danchouzhou/003Clock/firmware/ISP_UART1/isp_uart1.h

#define trig_IAPGO           TA=0xAA;TA=0x55;IAPTRG|=0x01

#define CMD_CONNECT          0xAE
#define CMD_SYNC_PACKNO      0xA4
#define CMD_GET_FWVER        0xA6
#define FW_VERSION           0x28
#define CMD_RUN_APROM        0xAB
#define CMD_GET_DEVICEID     0xB1
#define CMD_ERASE_ALL        0xA3
#define CMD_READ_CONFIG      0xA2
#define CMD_UPDATE_CONFIG    0xA1
#define CMD_UPDATE_APROM     0xA0
#define PAGE_ERASE_AP        0x22
#define BYTE_READ_AP         0x00
#define BYTE_PROGRAM_AP      0x21
#define BYTE_READ_ID         0x0C
#define PAGE_ERASE_CONFIG    0xE2
#define BYTE_READ_CONFIG     0xC0
#define BYTE_PROGRAM_CONFIG  0xE1
#define READ_UID             0x04
#define PAGE_SIZE            128
#define APROM_SIZE           4*1024  

extern BIT volatile bUartDataReady;
extern BIT volatile g_timer0Over;
extern BIT volatile g_timer1Over;
extern BIT volatile g_progarmflag;
extern BIT BIT_TMP;

extern __xdata volatile uint8_t uart_rcvbuf[64];
extern __xdata volatile uint8_t uart_txbuf[64];
extern __data volatile uint8_t bufhead;
extern __data volatile uint16_t flash_address;
extern __data volatile uint16_t AP_size;
extern __data volatile uint8_t g_timer1Counter;
extern __data volatile uint8_t count;
extern __data volatile uint16_t g_timer0Counter;
extern __data volatile uint32_t g_checksum;
extern __data uint8_t PID_highB, PID_lowB, DID_highB, DID_lowB, CONF0, CONF1, CONF2, CONF4;
extern __data uint8_t recv_CONF0, recv_CONF1, recv_CONF2, recv_CONF4;
extern __data volatile uint32_t g_totalchecksum;

void MODIFY_HIRC(uint8_t u8HIRCSEL);
void TM0_ini(void);
void UART1_ini_115200_166MHz(void);
void Package_checksum(void);
void Send_64byte_To_UART1(void);
void READ_ID(void);
void READ_CONFIG(void);
